useti/Lilypad-TVbGone/Images/iii.jpeg

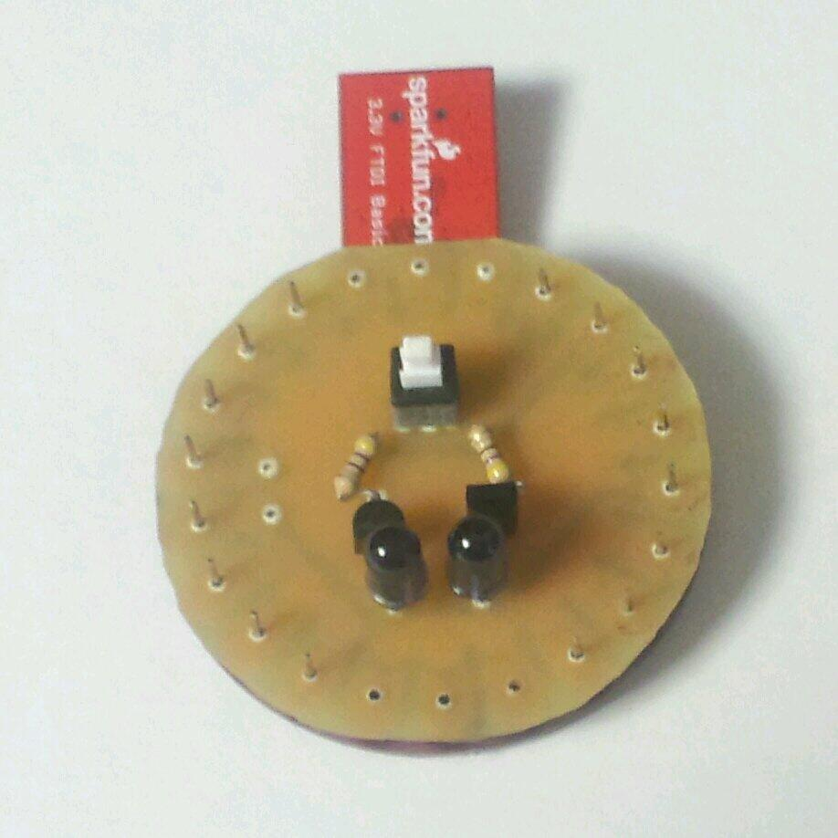
Images/iii.jpeg
