useti/Lilypad-TVbGone/Images/iv.png

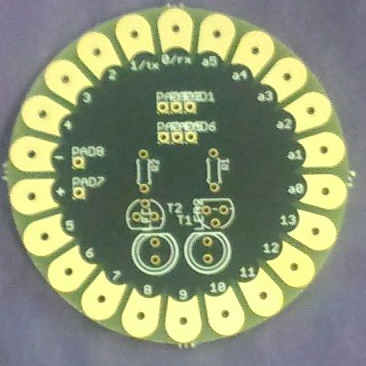
Images/iv.png
